nateo87/TTL-1-bit-Video-Board/gallery/2022-11-23.png

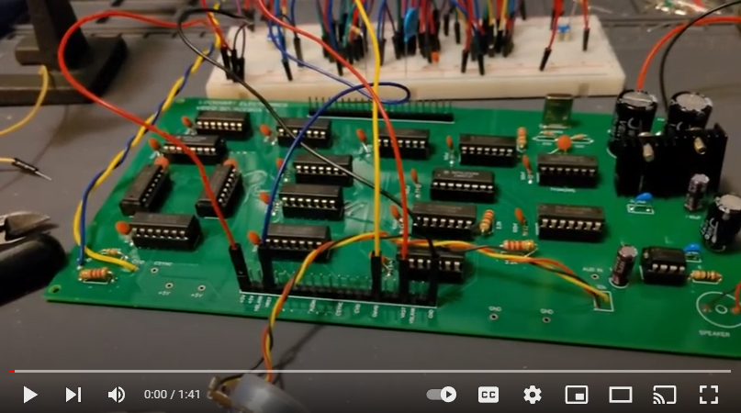
gallery/2022-11-23.png
